adafruit/TV-B-Gone-kit/firmware/WORLDcodes.c

#include <avr/io.h>
#include <avr/pgmspace.h>
#include "main.h"

//Codes captured from Generation 3 TV-B-Gone by Limor Fried & Mitch Altman
// table of POWER codes


#ifdef NA_CODES
const uint16_t code_na000Times[] PROGMEM = {
        60, 60,
        60, 2700,
        120, 60,
        240, 60,
};
const struct IrCode code_na000Code PROGMEM = {
        freq_to_timerval(38400),
        26,             // # of pairs
        2,              // # of bits per index
        code_na000Times,
        {
                0xE2,
                0x20,
                0x80,
                0x78,
                0x88,
                0x20,
                0x10,
        }
};

const uint16_t code_na001Times[] PROGMEM = {
	50, 100,
	50, 200,
	50, 800,
	400, 400,
};
const struct IrCode code_na001Code PROGMEM = {
	freq_to_timerval(57143),
	52,		// # of pairs
	2,		// # of bits per index
	code_na001Times,  
	{
		0xD5,
		0x41,
		0x11,
		0x00,
		0x14,
		0x44,
		0x6D,
		0x54,
		0x11,
		0x10,
		0x01,
		0x44,
		0x45,
	}
};
const uint16_t code_na002Times[] PROGMEM = {
	42, 46,
	42, 133,
	42, 7519,
	347, 176,
	347, 177,
};
const struct IrCode code_na002Code PROGMEM = {
	freq_to_timerval(37037),
	100,		// # of pairs
	3,		// # of bits per index
	code_na002Times,  
	{
		0x60,
		0x80,
		0x00,
		0x00,
		0x00,
		0x08,
		0x00,
		0x00,
		0x00,
		0x20,
		0x00,
		0x00,
		0x04,
		0x12,
		0x48,
		0x04,
		0x12,
		0x48,
		0x2A,
		0x02,
		0x00,
		0x00,
		0x00,
		0x00,
		0x20,
		0x00,
		0x00,
		0x00,
		0x80,
		0x00,
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
	&code_eu079Code,
	&code_eu080Code,
	&code_eu081Code,
	&code_eu082Code,
	&code_eu083Code,
	&code_eu084Code,
	&code_eu085Code,
	&code_eu086Code,
	&code_eu087Code,
	&code_eu088Code,
	&code_eu089Code,
	&code_eu090Code,
	&code_eu091Code,
	&code_eu092Code,
	&code_eu093Code,
	&code_eu094Code,
	&code_eu095Code,
	&code_eu096Code,
	&code_eu097Code,
	&code_eu098Code,
	&code_eu099Code,
	&code_eu100Code,
	&code_eu101Code,
	&code_eu102Code,
	&code_eu103Code,
	&code_eu104Code,
	&code_eu105Code,
	&code_eu106Code,
	&code_eu107Code,
	&code_eu108Code,
	&code_eu109Code,
	&code_eu110Code,
	&code_eu111Code,
	&code_eu112Code,
	&code_eu113Code,
	&code_eu114Code,
#ifndef NA_CODES
	&code_eu115Code,
	&code_eu116Code,
	&code_eu117Code,
	&code_eu118Code,
	&code_eu119Code,
	&code_eu120Code,
	&code_eu121Code,
	&code_eu122Code,
	&code_eu123Code,
	&code_eu124Code,
	&code_eu125Code,
	&code_eu126Code,
	&code_eu127Code,
	&code_eu128Code,
	&code_eu129Code,
	&code_eu130Code,
	&code_eu131Code,
	&code_eu132Code,
	&code_eu133Code,
	&code_eu134Code,
	&code_eu135Code,
	&code_eu136Code,
	&code_eu137Code,
	&code_eu138Code,
	&code_eu139Code,
#endif
#endif
};

const uint8_t num_NAcodes = NUM_ELEM(NApowerCodes);
const uint8_t num_EUcodes = NUM_ELEM(EUpowerCodes);
